RW-FPGA-devel-Team/Rememotech-Mister/doc/altera-de1.jpg

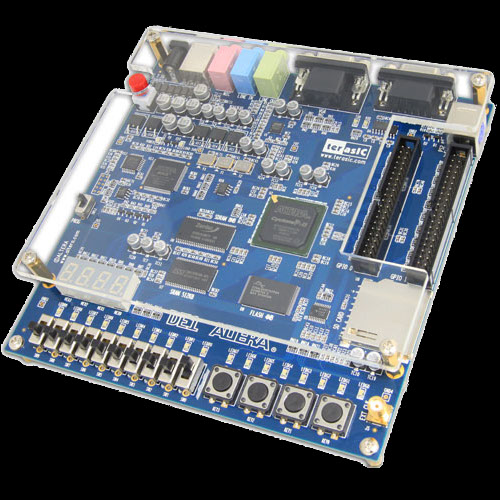
doc/altera-de1.jpg
