RW-FPGA-devel-Team/Rememotech-Mister/doc/daughter-3d.jpg

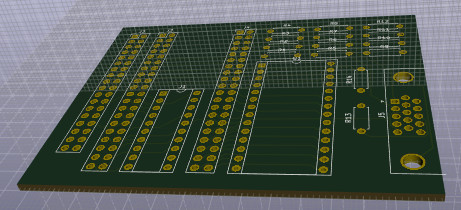
doc/daughter-3d.jpg
