RW-FPGA-devel-Team/Rememotech-Mister/rtl/mon_prom_alpha.vhd

--
-- mon_prom_alpha.vhd - Alpha character generator
--
-- This is the 80 column character set.
-- The first row of each of the 256 characters is stored,
-- then the next row of each, etc..
-- In this way, addressing is row&char (no multiply by 10 needed)
--
-- This is a synchronous implementation
--

library IEEE;
use IEEE.STD_LOGIC_1164.ALL;
use IEEE.NUMERIC_STD.ALL;

entity mon_prom_alpha is
  port
    (
    clk  : in  std_logic;
    addr : in  std_logic_vector(11 downto 0);
    q    : out std_logic_vector(07 downto 0)
    );
end mon_prom_alpha;

architecture behavior of mon_prom_alpha is

  type rom_type is array (0 to 2559) of std_logic_vector(7 downto 0);

  function init_rom return rom_type is
    variable r : rom_type := (others => (others => 'X'));
  begin
    r(   0) := "00000000";
    r(   1) := "00000000";
    r(   2) := "00000000";
    r(   3) := "00000000";
    r(   4) := "00000000";
    r(   5) := "00000000";
    r(   6) := "00000000";
    r(   7) := "00000000";
    r(   8) := "00000000";
    r(   9) := "00000000";
    r(  10) := "00000000";
    r(  11) := "00000000";
    r(  12) := "00000000";
    r(  13) := "00000000";
    r(  14) := "00000000";
    r(  15) := "00000000";
    r(  16) := "00000000";
    r(  17) := "00000000";
    r(  18) := "00000000";
    r(  19) := "00000000";
    r(  20) := "00000000";
    r(  21) := "00000000";
    r(  22) := "00000000";
    r(  23) := "00000000";
    r(  24) := "00000000";
    r(  25) := "00000000";
    r(  26) := "00000000";
    r(  27) := "00000000";
    r(  28) := "00000000";
    r(  29) := "00000000";
    r(  30) := "00000000";
    r(  31) := "00000000";
    r(  32) := "00000000";
    r(  33) := "00000000";
    r(  34) := "00000000";
    r(  35) := "00000000";
    r(  36) := "00000000";
    r(  37) := "00000000";
    r(  38) := "00000000";
    r(  39) := "00000000";
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
    return r;
  end init_rom;

  -- Quartus II should notice this and create a .mif file
  signal rom : rom_type := init_rom;

  -- Ensure Quartus II doesn't try to infer an ALTSYNCRAM
  -- as we'd overflow our 26 M4K budget, so instead use LEs
--  attribute ramstyle : string;
--  attribute ramstyle of rom : signal is "logic";

begin

  process ( clk )
  begin
    if rising_edge(clk) then
      q <= rom(to_integer(unsigned(addr)));
    end if;
  end process;

end behavior;
