RW-FPGA-devel-Team/Rememotech-Mister/rtl/RamRom/RamRom_inst.v

RamRom	RamRom_inst (
	.address ( address_sig ),
	.byteena ( byteena_sig ),
	.clken ( clken_sig ),
	.clock ( clock_sig ),
	.data ( data_sig ),
	.rden ( rden_sig ),
	.wren ( wren_sig ),
	.q ( q_sig )
	);
