RW-FPGA-devel-Team/Rememotech-Mister/boot/reboot.vhd

    r(0) := x"f3";
    r(1) := x"31";
    r(2) := x"00";
    r(3) := x"ff";
    r(4) := x"cd";
    r(5) := x"45";
    r(6) := x"00";
    r(7) := x"db";
    r(8) := x"c5";
    r(9) := x"f5";
    r(10) := x"cb";
    r(11) := x"57";
    r(12) := x"cc";
    r(13) := x"8a";
    r(14) := x"00";
    r(15) := x"f1";
    r(16) := x"f5";
    r(17) := x"cb";
    r(18) := x"4f";
    r(19) := x"cc";
    r(20) := x"36";
    r(21) := x"01";
    r(22) := x"f1";
    r(23) := x"cb";
    r(24) := x"47";
    r(25) := x"cc";
    r(26) := x"40";
    r(27) := x"01";
    r(28) := x"3e";
    r(29) := x"08";
    r(30) := x"d3";
    r(31) := x"d0";
    r(32) := x"21";
    r(33) := x"00";
    r(34) := x"60";
    r(35) := x"11";
    r(36) := x"3d";
    r(37) := x"00";
    r(38) := x"06";
    r(39) := x"08";
    r(40) := x"1a";
    r(41) := x"be";
    r(42) := x"20";
    r(43) := x"0c";
    r(44) := x"13";
    r(45) := x"23";
    r(46) := x"10";
    r(47) := x"f8";
    r(48) := x"af";
    r(49) := x"d3";
    r(50) := x"c0";
    r(51) := x"d3";
    r(52) := x"c1";
    r(53) := x"c3";
    r(54) := x"08";
    r(55) := x"60";
    r(56) := x"3e";
    r(57) := x"ff";
    r(58) := x"c3";
    r(59) := x"5d";
    r(60) := x"02";
    r(61) := x"52";
    r(62) := x"45";
    r(63) := x"4d";
    r(64) := x"4f";
    r(65) := x"4e";
    r(66) := x"35";
    r(67) := x"31";
    r(68) := x"32";
    r(69) := x"3e";
    r(70) := x"0c";
    r(71) := x"d3";
    r(72) := x"38";
    r(73) := x"af";
    r(74) := x"d3";
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
    r(626) := x"cb";
    r(627) := x"15";
    r(628) := x"cb";
    r(629) := x"14";
    r(630) := x"3e";
    r(631) := x"11";
    r(632) := x"cd";
    r(633) := x"23";
    r(634) := x"02";
    r(635) := x"06";
    r(636) := x"ff";
    r(637) := x"cd";
    r(638) := x"50";
    r(639) := x"02";
